mgesteiro/focoir/fotos/ATtiny85-portadora.jpg

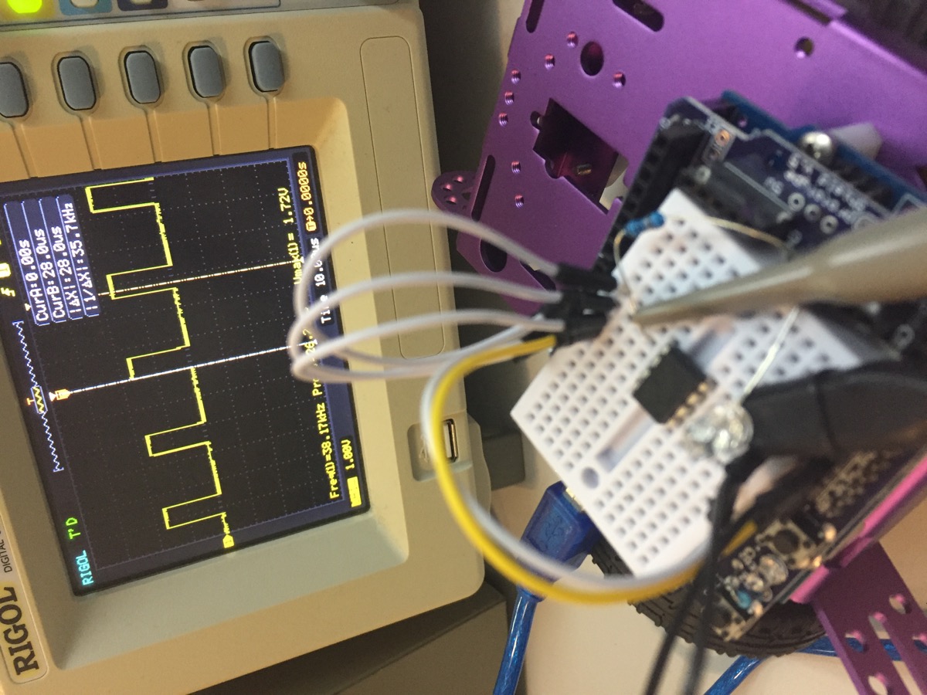
fotos/ATtiny85-portadora.jpg
