mgesteiro/focoir/fotos/eprom01.jpg

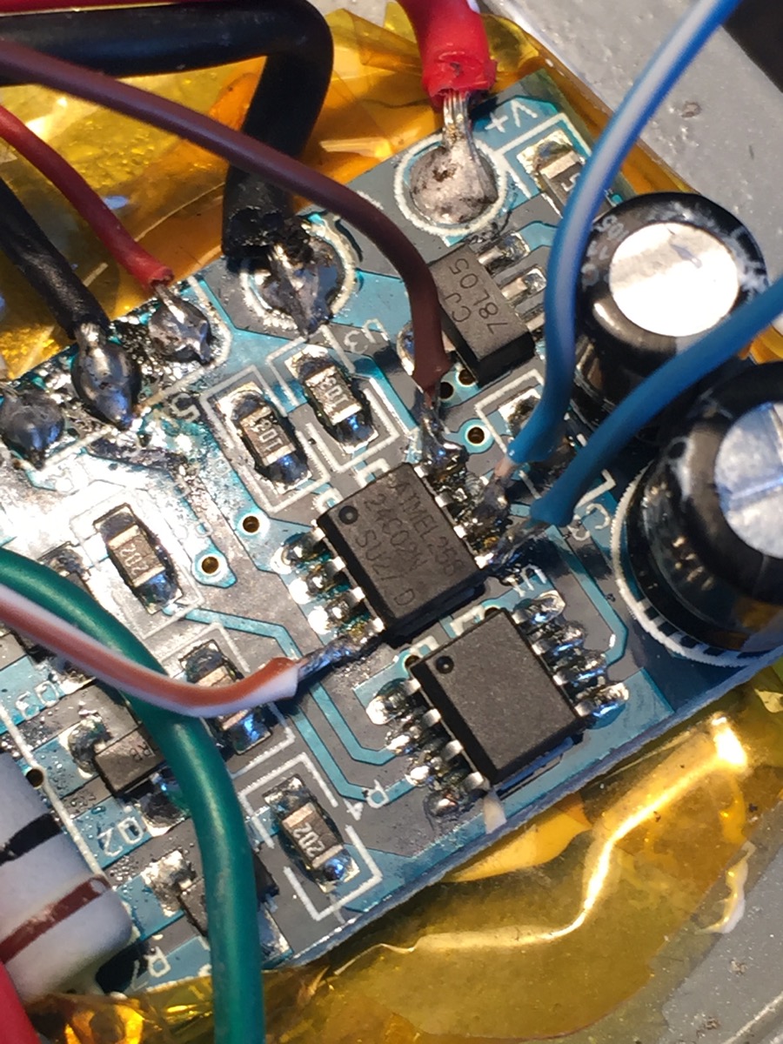
fotos/eprom01.jpg
