mgesteiro/focoir/fotos/eprom02.jpg

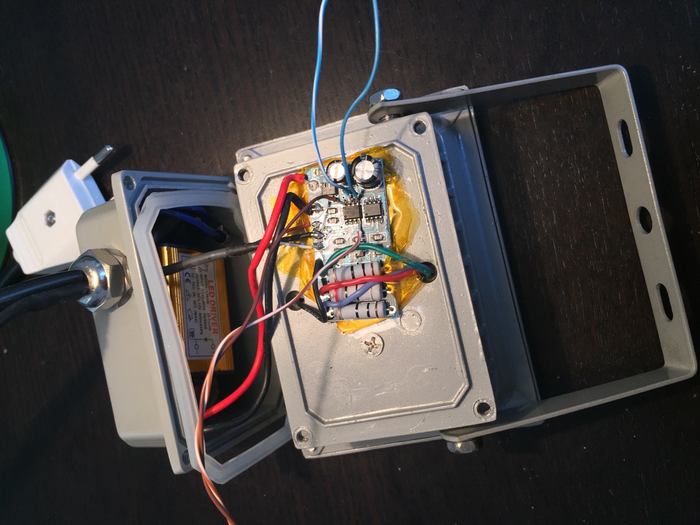
fotos/eprom02.jpg
