mgesteiro/focoir/fotos/foco03.jpg

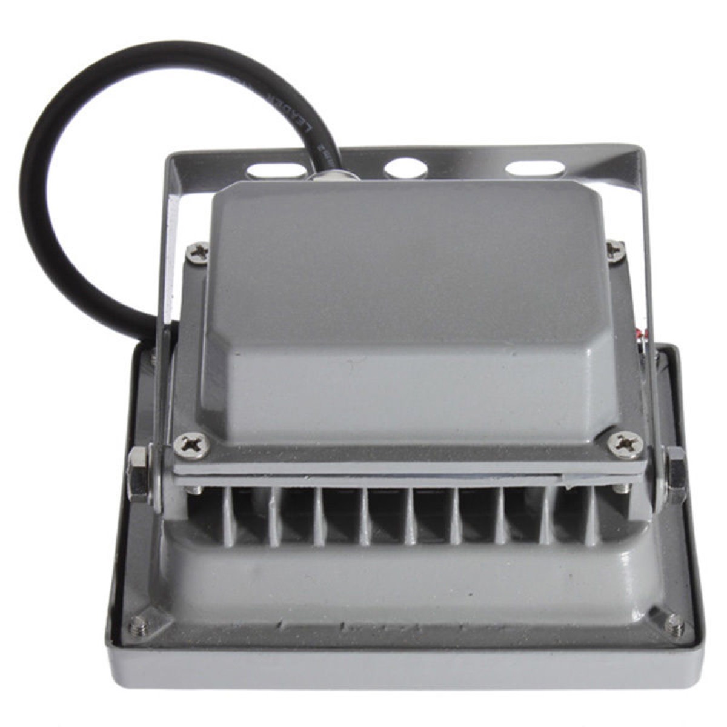
fotos/foco03.jpg
