mgesteiro/focoir/fotos/mifoco01.jpg

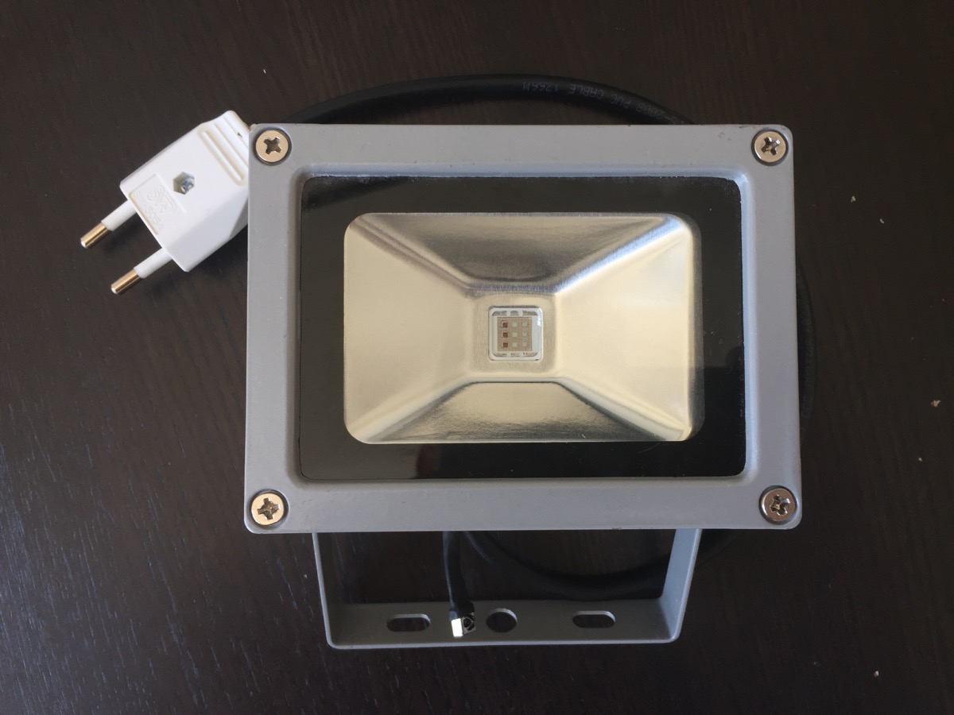
fotos/mifoco01.jpg
