mgesteiro/focoir/fotos/mifoco02.jpg

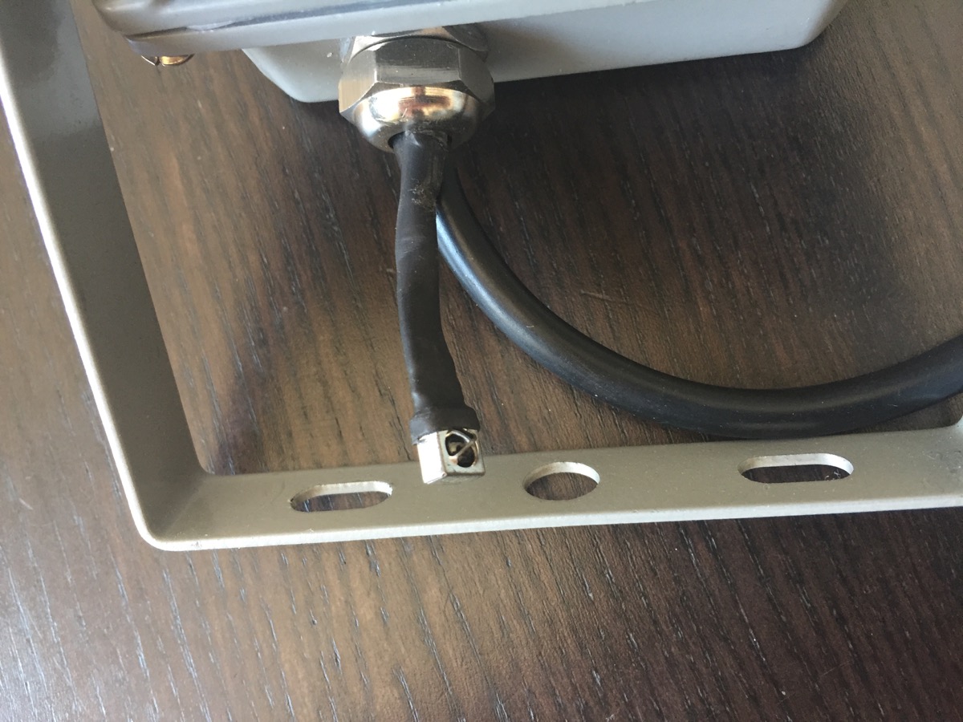
fotos/mifoco02.jpg
