mgesteiro/focoir/fotos/IRDebug.jpg

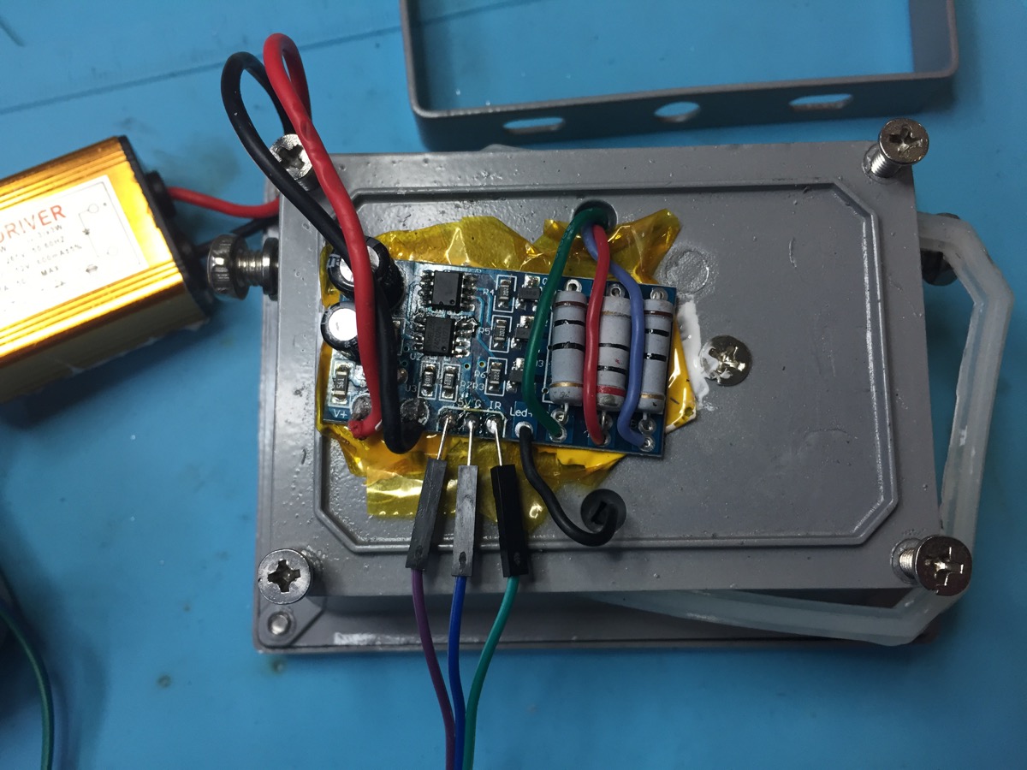
fotos/IRDebug.jpg
